fabiosoft/esp8266_ikea_vindriktning/PCB/IMG_0475.jpg

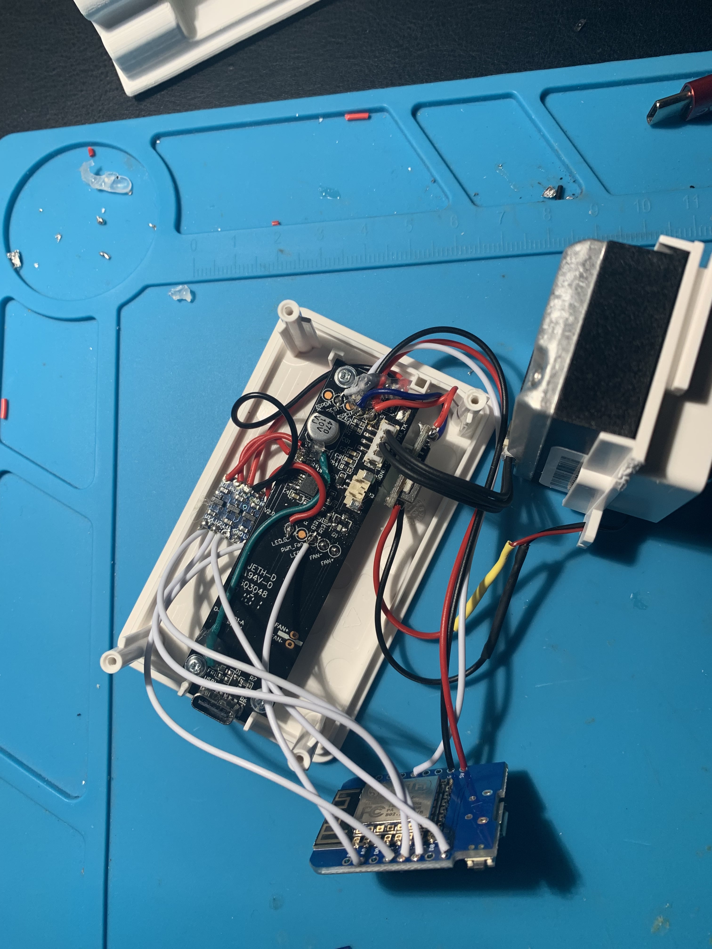
PCB/IMG_0475.jpg
